karafamichal/lixie-stopwatch/nextion-stopwatch/weather.h

#ifndef WEATHER_H
#define WEATHER_H

#include <Arduino.h>

struct WeatherInfo {
    bool     valid        = false;
    String   city;
    float    tempC        = 0;
    int      wmoCode      = -1;   // Open-Meteo weathercode; label via Lang::weather()
    uint32_t lastUpdateMs = 0;
};

namespace Weather {

// Blocking — does an IP lookup (ip-api.com) on first call to learn lat/lon,
// then queries Open-Meteo for current temperature + weather code. Updates
// the cached WeatherInfo. Returns true on success.
bool refresh();

const WeatherInfo& get();

}  // namespace Weather

#endif
